CISSROV/2020-Project/STLs/Engine Mount Holder rev2_Left Hole.stl

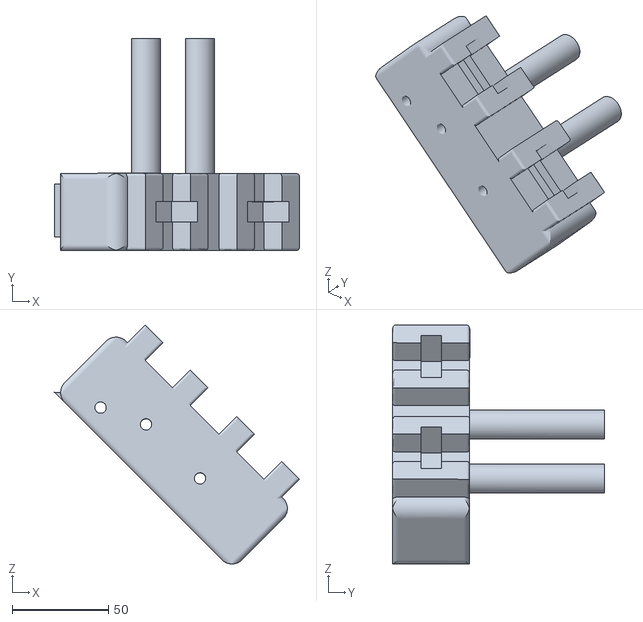
[picture p19: CAD file, 2019-02-01]
STLs/Engine Mount Holder rev2_Left Hole.stl
127.0 x 110.1 x 123.9
