CISSROV/2020-Project/STLs/Camera Mount Below Bottom Piece.stl

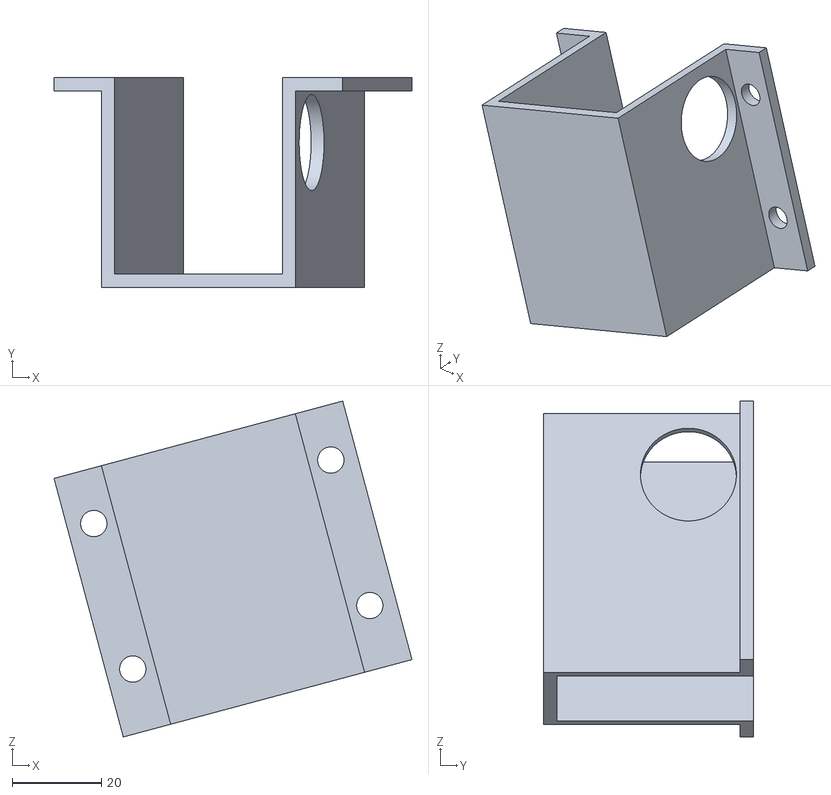
[picture p20: CAD file, 2019-01-28]
STLs/Camera Mount Below Bottom Piece.stl
80.2 x 47.0 x 75.3
