CISSROV/2020-Project/STLs/Camera Mount Top Forward_Bottom Piece.stl

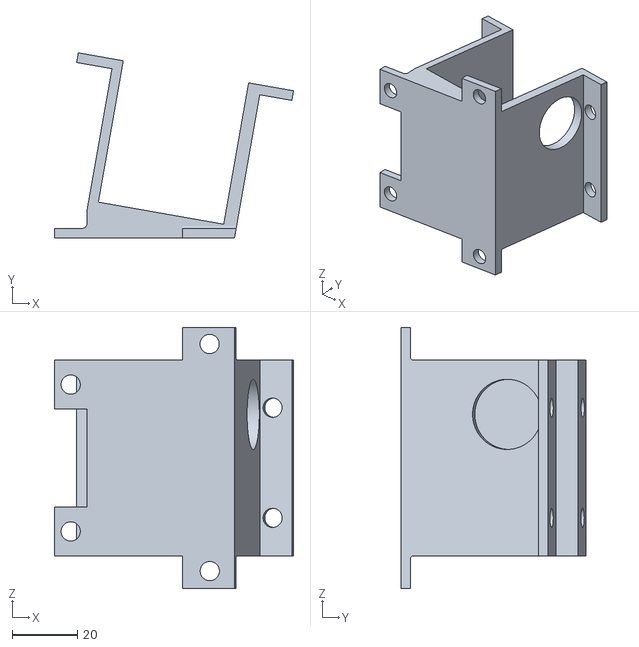
[picture p21: CAD file, 2019-01-23]
STLs/Camera Mount Top Forward_Bottom Piece.stl
73.3 x 56.8 x 80.0
