CISSROV/2020-Project/STLs/Tube Mount v2.stl

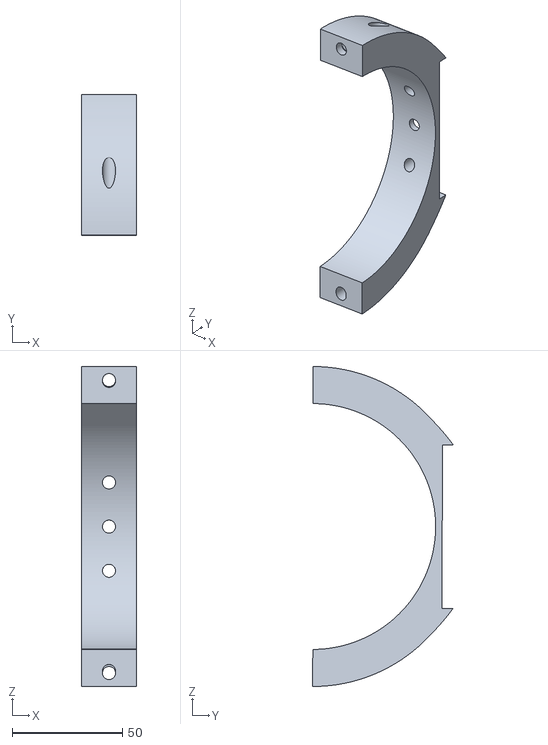
[picture p22: CAD file, 2019-01-21]
STLs/Tube Mount v2.stl
25.0 x 63.7 x 144.9
