CISSROV/2020-Project/code/core/JoshuaClient.py

import sys
import socket
import select
import pygame
import time
import serial as s
import threading
from serial import SerialException
# import pyfirmata


########Below is superfluous code necessary only for receiving and sending controller input
pygame.init()

joystick1 = pygame.joystick.Joystick(0)
joystick2 = pygame.joystick.Joystick(1)
joystick1.init()
joystick2.init()


def print_data():

    data = []

    for x in range(6):
        data.append(joystick1.get_axis(x))

    data.append(joystick1.get_button(4))
    data.append(joystick1.get_button(5))
        
    for x in range(6):
        data.append(joystick2.get_axis(x))

    data.append(joystick2.get_button(4))
    data.append(joystick2.get_button(5))

    mesg = ''
    for x in range(len(data)):
        data[x] = round(data[x], 2)
        mesg += str(data[x])
        mesg += " "
    
    
##    data = joystick1.get_axis(0)
##    data2 = joystick1.get_axis(1)
##    data3 = joystick1.get_axis(2)
##    data4 = joystick1.get_axis(3)    
##    data5 = joystick1.get_axis(4)
##    data6 = joystick1.get_axis(5)
##    data7 = joystick1.get_button(10)
##    data8 = joystick2.get_button(1)
##    data9 = joystick2.get_axis(0)
##
##    data = round(data, 2)
##    data2 = round(data2, 2)
##    data3 = round(data3, 2)
##    data4 = round(data4, 2)
##    data5 = round(data5, 2)
##    data6 = round(data6, 2)
##    data9 = round(data9, 2)
##    mesg = str(data) + " " + str(data2) + " " + str(data3) + " " + str(data4) + " " + str(data5) + " " + str(data6) +" "+str(data7) + " " + str(data7) + " " + str(data8) + " " + str(data9)
##    # print msg
##
    
    pygame.event.pump()
    time.sleep(0.05)
        
    return mesg
        

# #setup pyFirmata
# board =  pyfirmata.Arduino('/dev/cu.usbmodem1421')

# #setup an iterator for safety
# iter8 = pyfirmata.util.Iterator(board)
# iter8.start()

# #locate pins
# pin9 = board.get_pin('d:9:s') #motor 1
# # pin8 = board.get_pin('d:8:s') #motor 2

# def move1(a):
#     pin9.write(a)

# def move2(a):
#     pin8.write(a)

########Multiple clients connect to a server than send and receive data to all clients
def chat_client(host='192.168.1.82',port=9009):
    if (host == None or port == None):
    if(len(sys.argv) < 3) :
            print 'Usage : python chat_client.py hostname port'
            sys.exit()
        host = sys.argv[1]
        port = int(sys.argv[2])
    
    s = socket.socket(socket.AF_INET, socket.SOCK_STREAM)
    s.settimeout(2)
     
    # connect to remote host
    try :
        s.connect((host, port))
    except :
        print 'Unable to connect'
        sys.exit()
     
    print 'Connected to remote host. You can start sending messages'
    sys.stdout.write('[Me] '); sys.stdout.flush()
     
    while 1:
        socket_list = [sys.stdin, s]
         
        # Get the list sockets which are readable
        ready_to_read,ready_to_write,in_error = select.select(socket_list , [], [])
         
        for sock in ready_to_read:             
            if sock == s:
                # incoming message from remote server, s
                data = sock.recv(4096)
                if not data :
                    print '\nDisconnected from chat server'
                    sys.exit()
                else :
                    #print data
            sys.stdout.write(data)
                    sys.stdout.write('[Me] '); sys.stdout.flush()     
            
            else :
                # user entered a message
        msg = print_data()
                s.send(msg)
                sys.stdout.write(msg + '\n[Me]'); sys.stdout.flush() 
                
                
t1 = threading.Thread(target = chat_client)
t1.start()
